JTrillo/TFG/HW/images/2-TMP/a.jpeg

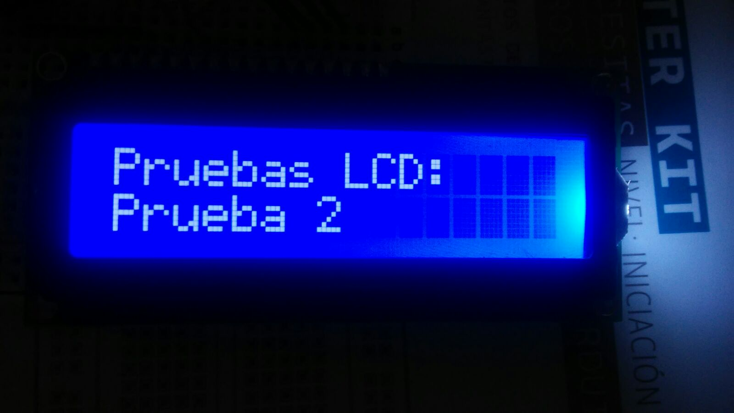
HW/images/2-TMP/a.jpeg
