JTrillo/TFG/HW/images/2-TMP/b.jpeg

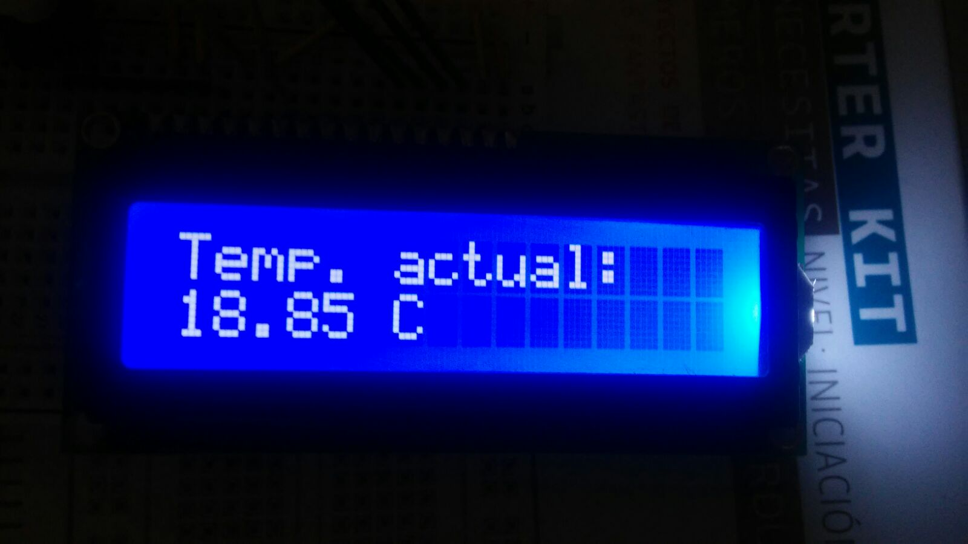
HW/images/2-TMP/b.jpeg
