JTrillo/TFG/HW/images/3-Hall/a.jpeg

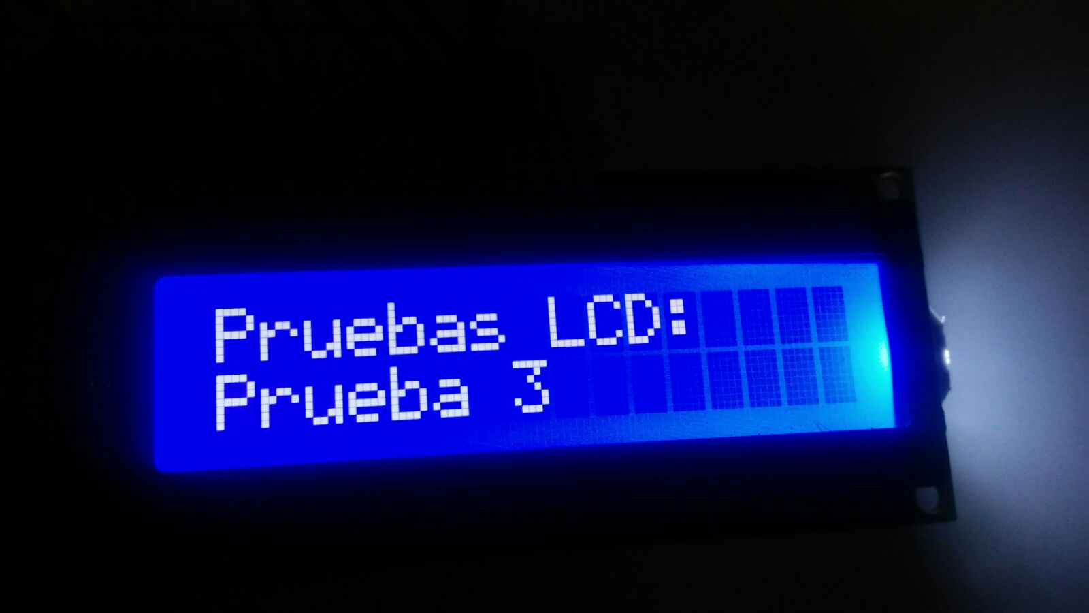
HW/images/3-Hall/a.jpeg
