JTrillo/TFG/HW/images/3-Hall/b.jpeg

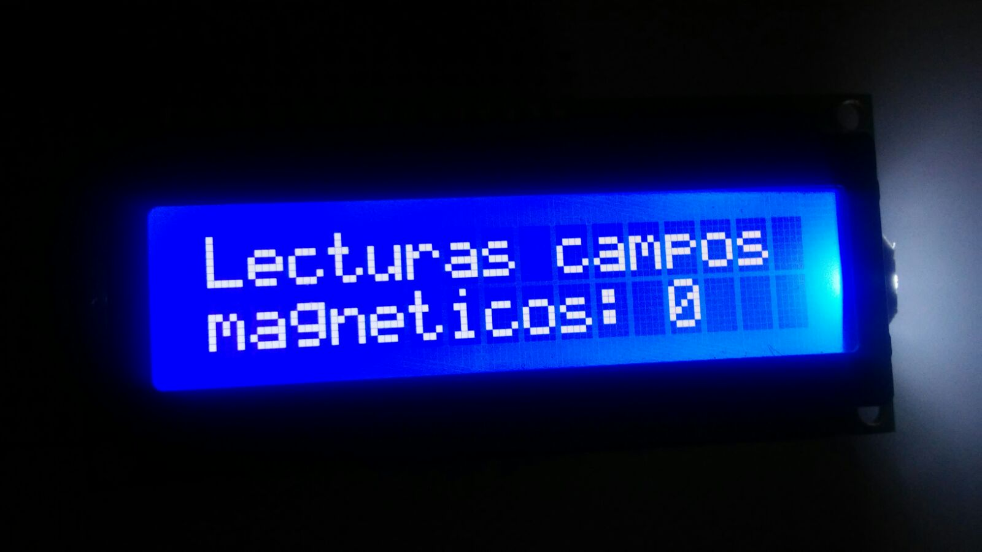
HW/images/3-Hall/b.jpeg
