JTrillo/TFG/HW/images/4-Ultrasonic/a.jpeg

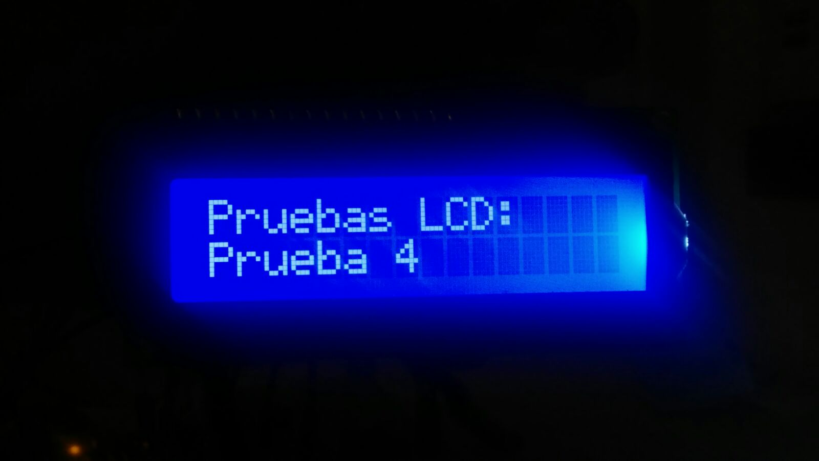
HW/images/4-Ultrasonic/a.jpeg
