JTrillo/TFG/HW/images/4-Ultrasonic/b.jpeg

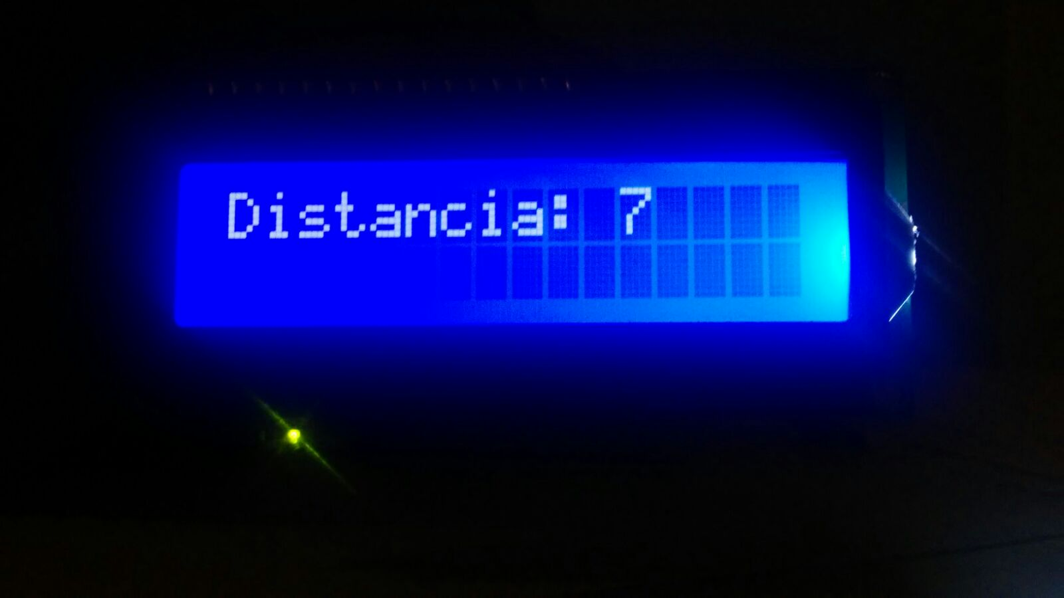
HW/images/4-Ultrasonic/b.jpeg
