JTrillo/TFG/HW/images/5-LED_matrix/a.jpeg

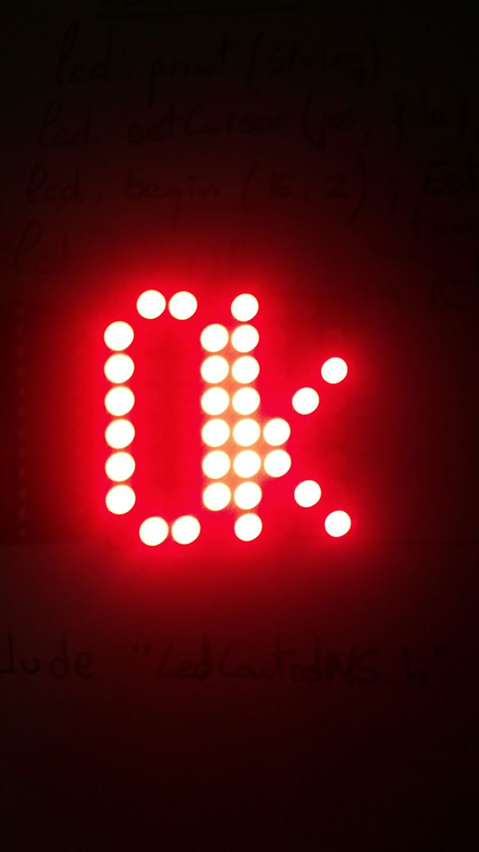
HW/images/5-LED_matrix/a.jpeg
