JTrillo/TFG/HW/images/5-LED_matrix/b.jpeg

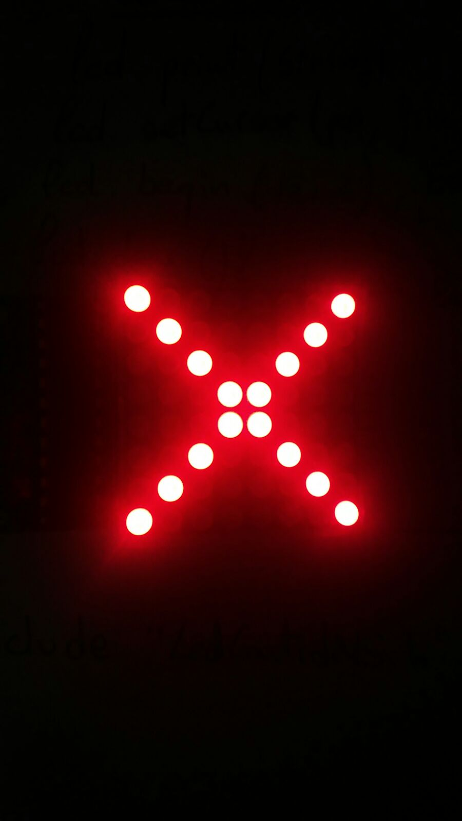
HW/images/5-LED_matrix/b.jpeg
