JTrillo/TFG/HW/images/6-Full_system/a.jpeg

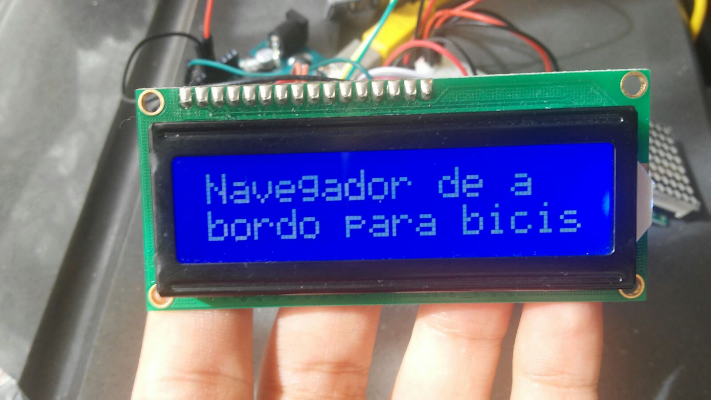
HW/images/6-Full_system/a.jpeg
