JTrillo/TFG/HW/images/6-Full_system/b.jpeg

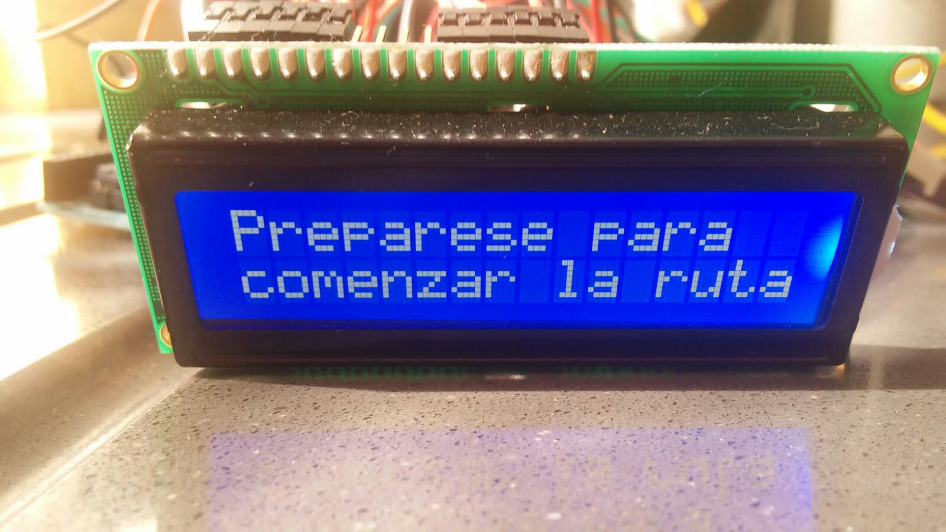
HW/images/6-Full_system/b.jpeg
