JTrillo/TFG/HW/images/6-Full_system/c.jpeg

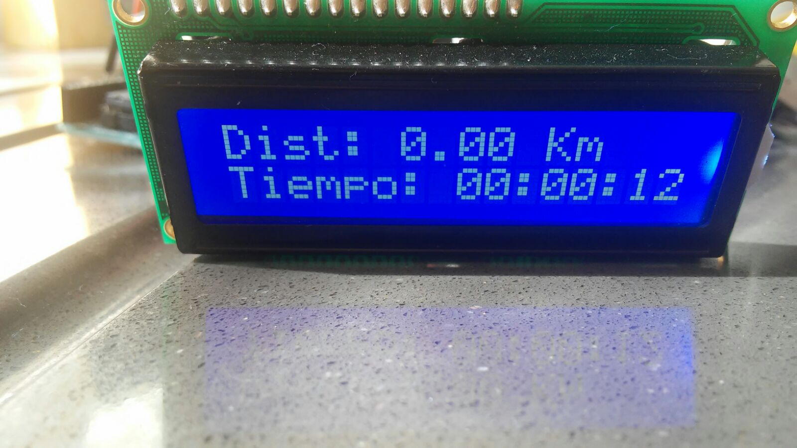
HW/images/6-Full_system/c.jpeg
