JTrillo/TFG/HW/images/6-Full_system/d.jpeg

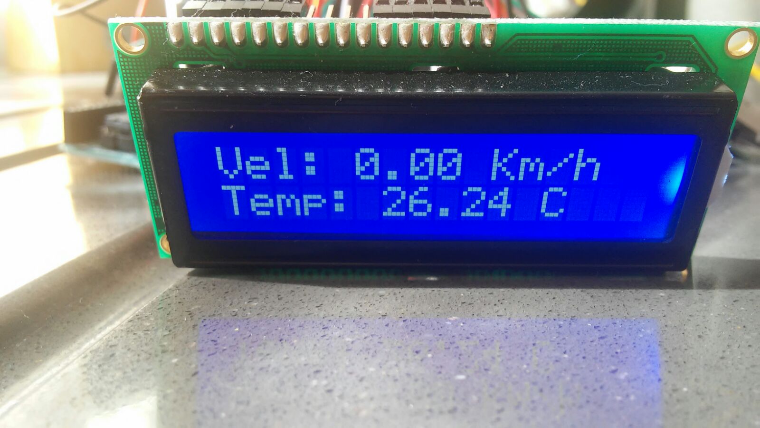
HW/images/6-Full_system/d.jpeg
