JTrillo/TFG/HW/images/6-Full_system/e.jpeg

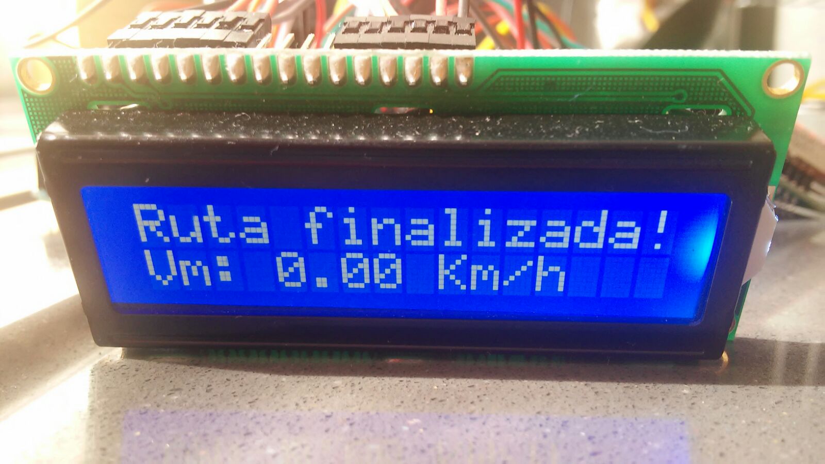
HW/images/6-Full_system/e.jpeg
