JTrillo/TFG/HW/images/6-Full_system/f.jpeg

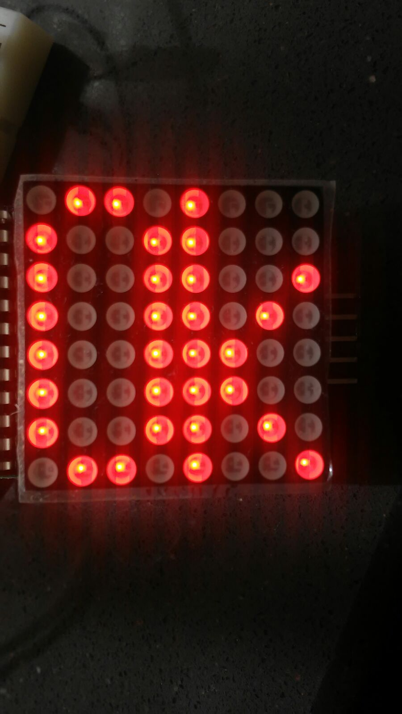
HW/images/6-Full_system/f.jpeg
