JTrillo/TFG/HW/images/6-Full_system/g.jpeg

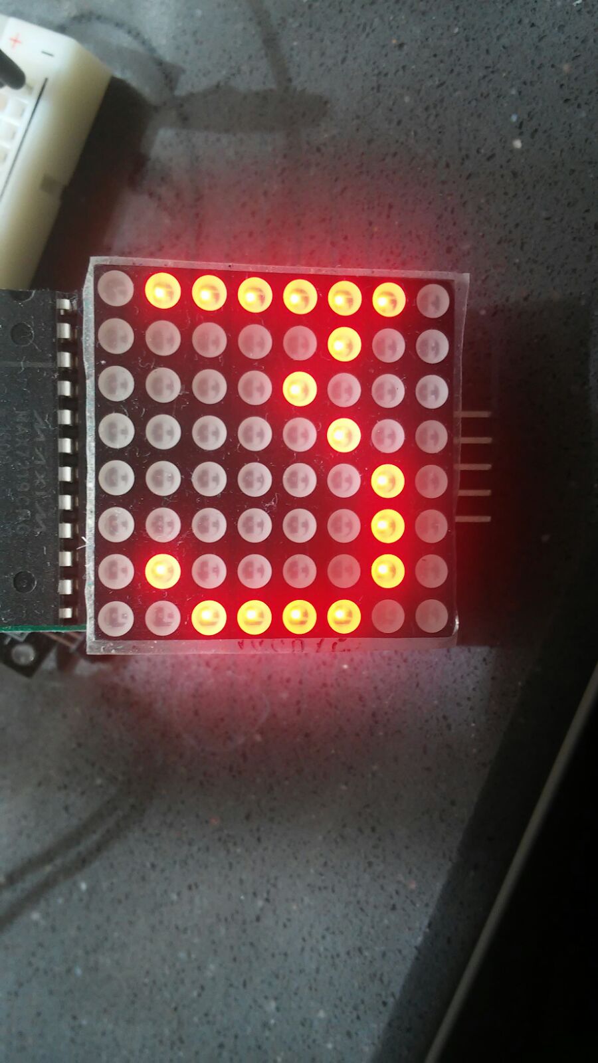
HW/images/6-Full_system/g.jpeg
