JTrillo/TFG/HW/images/6-Full_system/h.jpeg

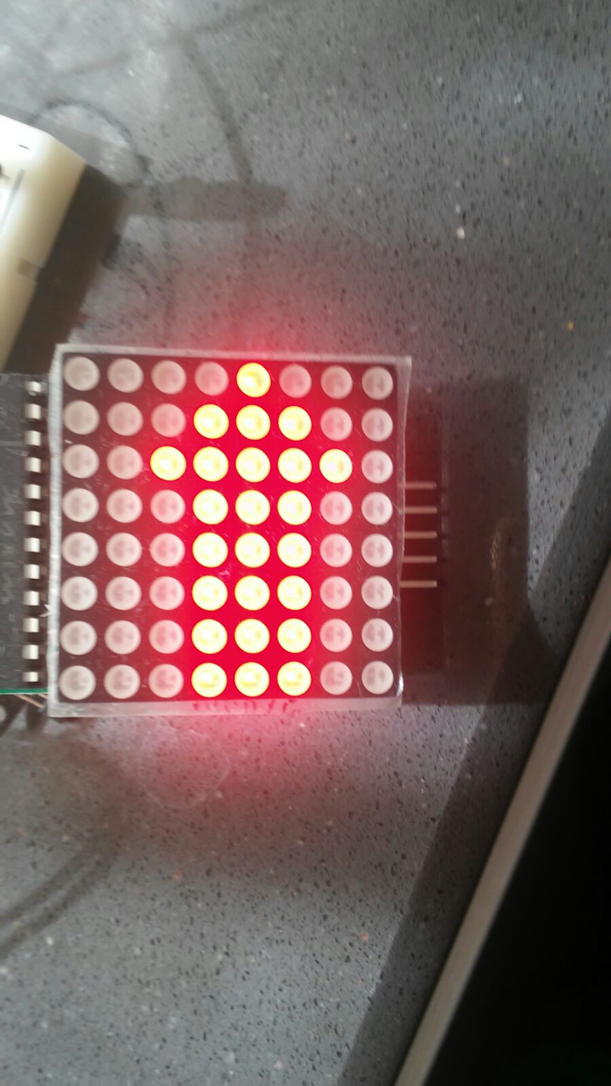
HW/images/6-Full_system/h.jpeg
