JTrillo/TFG/HW/images/6-Full_system/i.jpeg

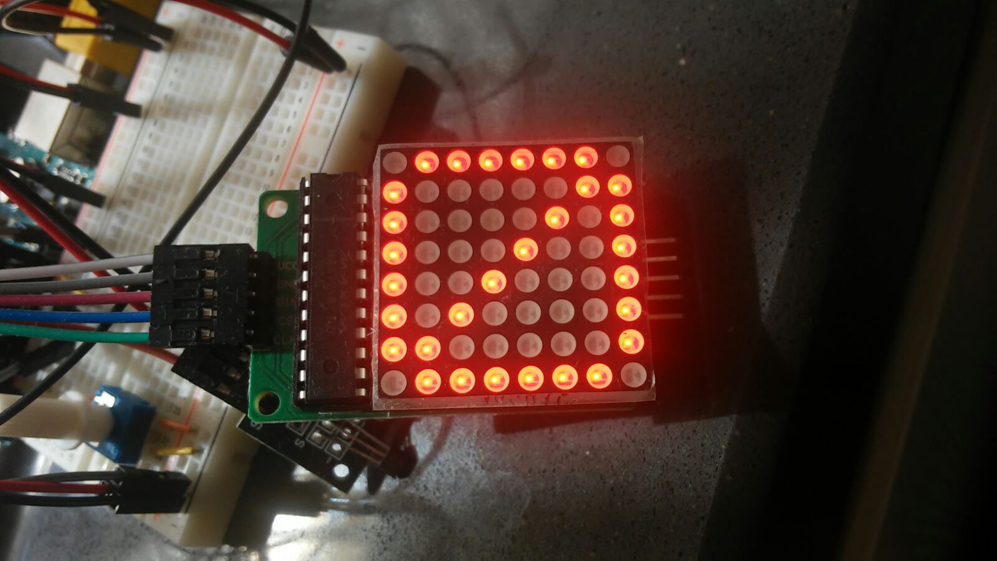
HW/images/6-Full_system/i.jpeg
