JTrillo/TFG/HW/schematics/1-LCD/schema-A.jpg

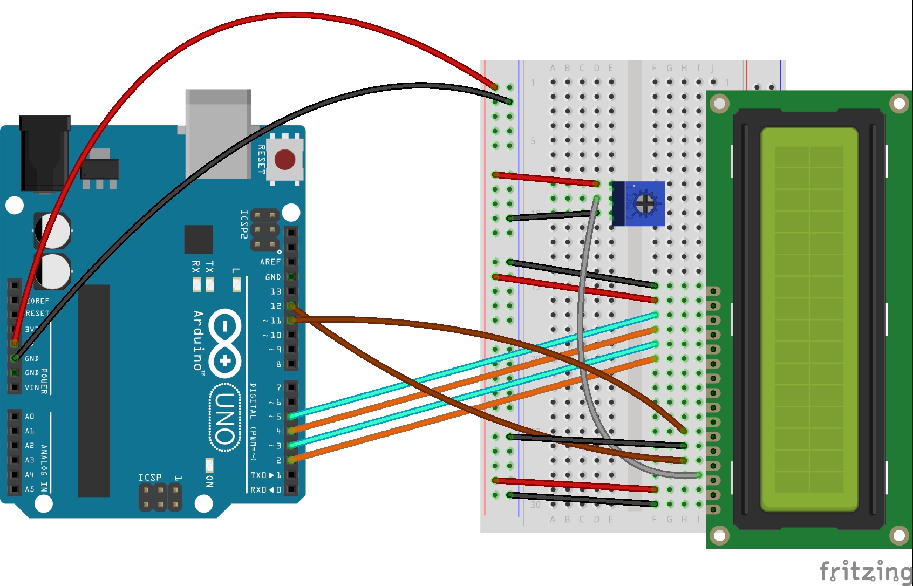
HW/schematics/1-LCD/schema-A.jpg
