JTrillo/TFG/HW/schematics/1-LCD/schema-B.jpg

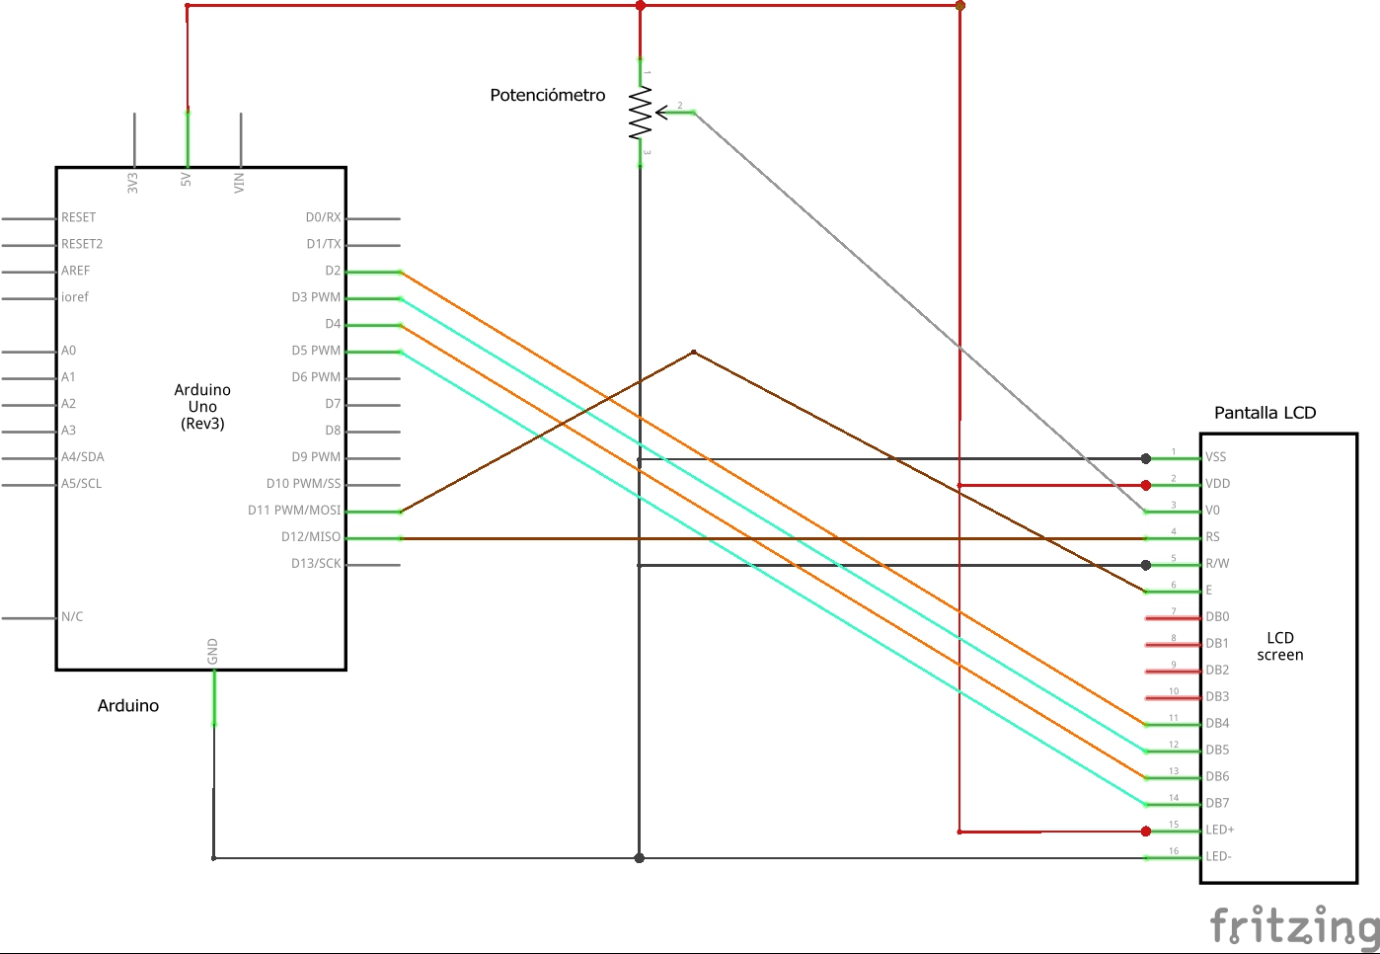
HW/schematics/1-LCD/schema-B.jpg
