JTrillo/TFG/HW/schematics/2-TMP/schema-B.jpg

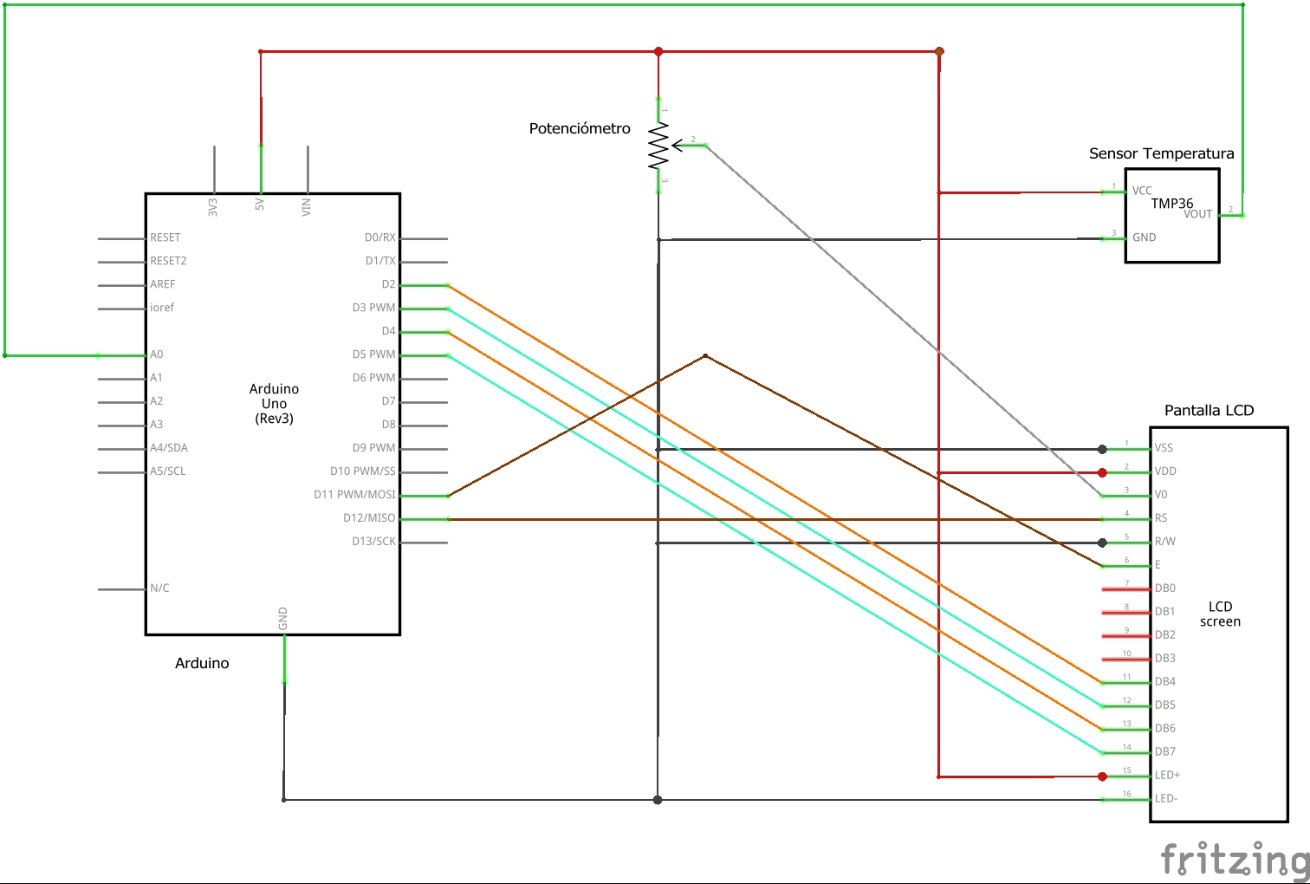
HW/schematics/2-TMP/schema-B.jpg
