JTrillo/TFG/HW/schematics/6-Full_system/schema-B.jpg

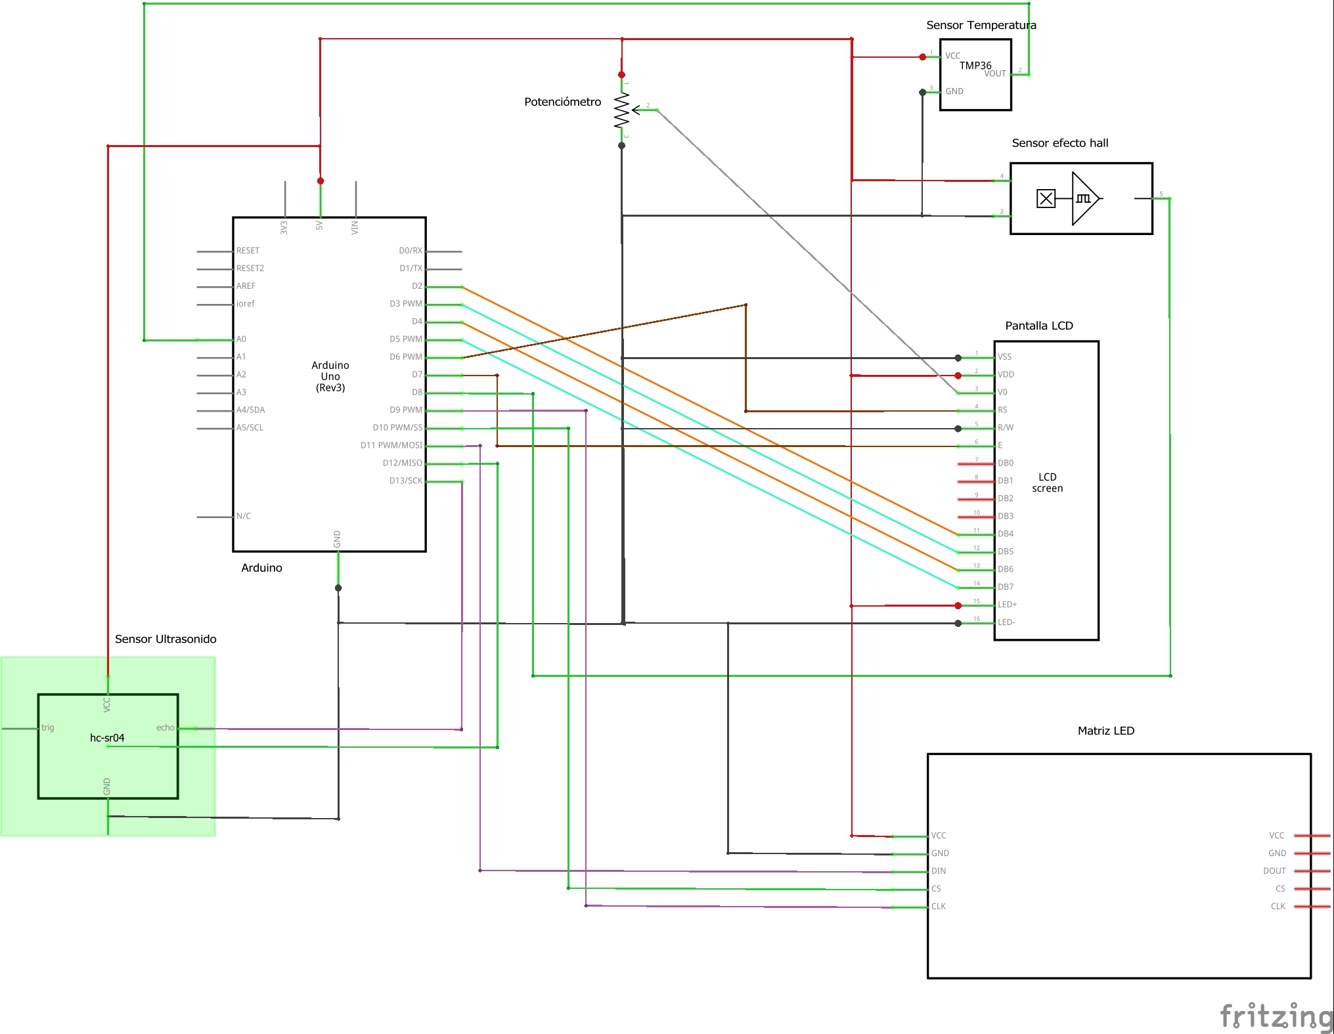
HW/schematics/6-Full_system/schema-B.jpg
