JTrillo/TFG/HW/firmware/_7-Bluetooth/_7-Bluetooth.ino

#include <SoftwareSerial.h> //Librería que permite establecer comunicación serie en otros pins
 
//Aquí conectamos los pins RXD,TDX del módulo Bluetooth.
SoftwareSerial BT(11,10); //10 RX, 11 TX.
 
void setup()
{
  BT.begin(9600); //Velocidad del puerto del módulo Bluetooth
  Serial.begin(9600); //Abrimos la comunicación serie con el PC y establecemos velocidad
}
 
void loop()
{
  if(BT.available())
  {
    Serial.write(BT.read());
  }
 
  if(Serial.available())
  {
     BT.write(Serial.read());
  }
}
